palazzol/TMS7xxx_dumper/images/DatabookDescribingSimilarInterface1.jpg

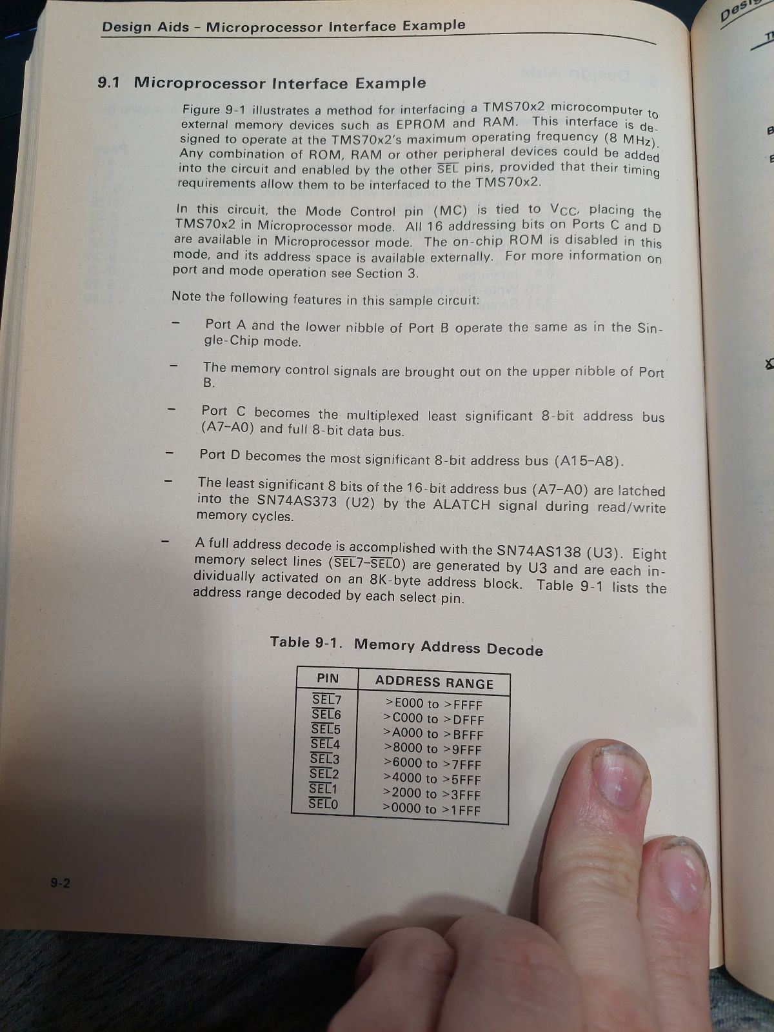
images/DatabookDescribingSimilarInterface1.jpg
