palazzol/TMS7xxx_dumper/images/DatabookDescribingSimilarInterface2.jpg

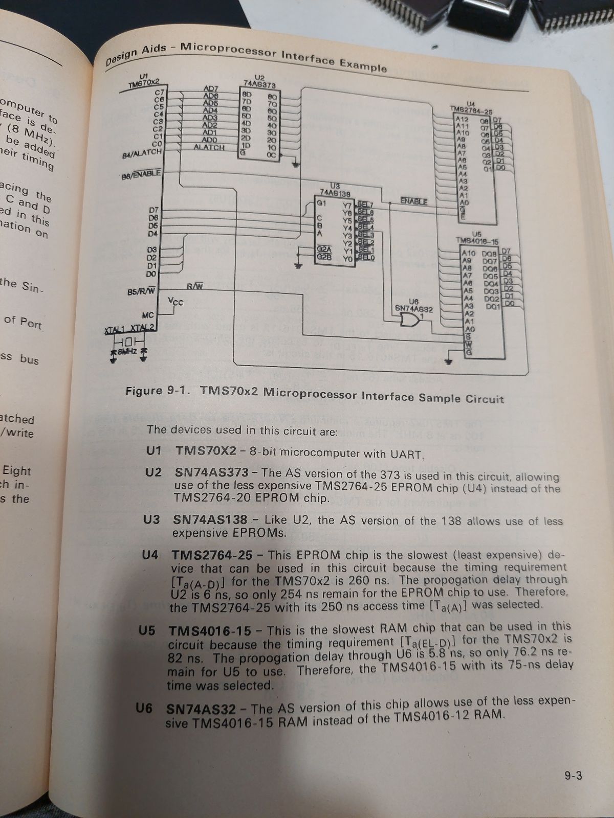
images/DatabookDescribingSimilarInterface2.jpg
