palazzol/TMS7xxx_dumper/images/latest databook excerpts/20230110_223147.jpg

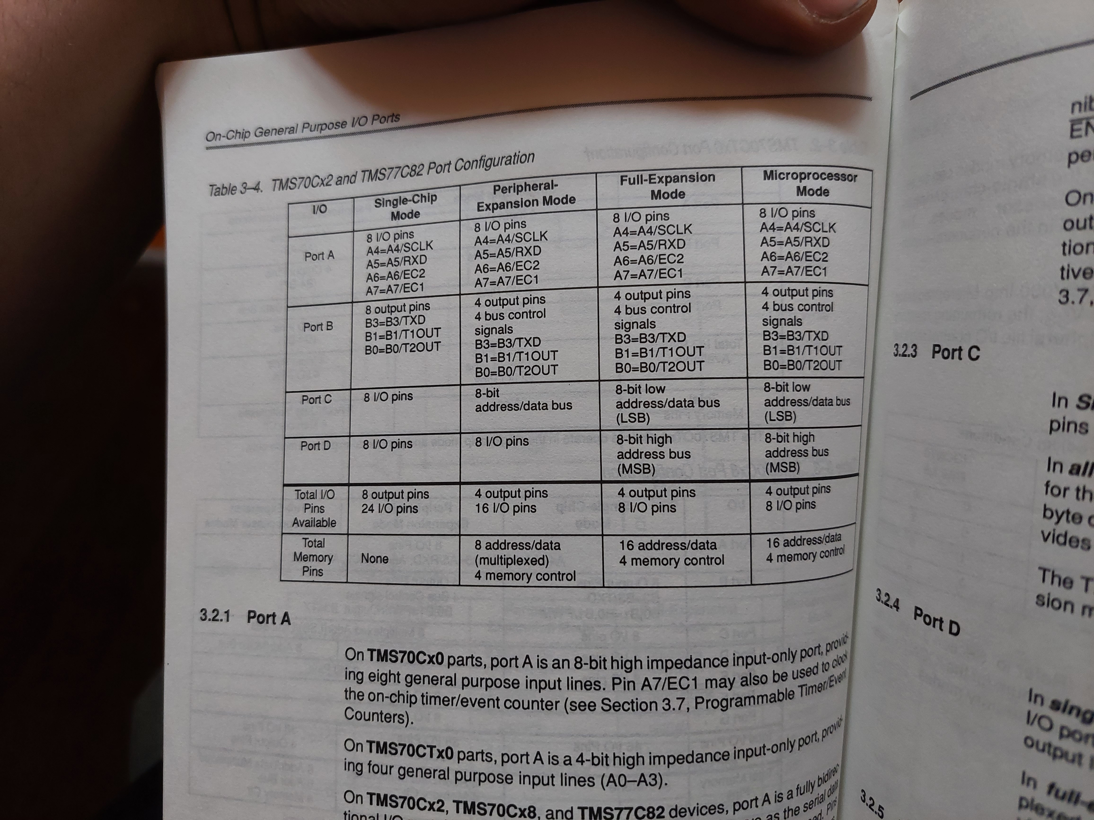
images/latest databook excerpts/20230110_223147.jpg
