palazzol/TMS7xxx_dumper/images/latest databook excerpts/20230110_223242.jpg

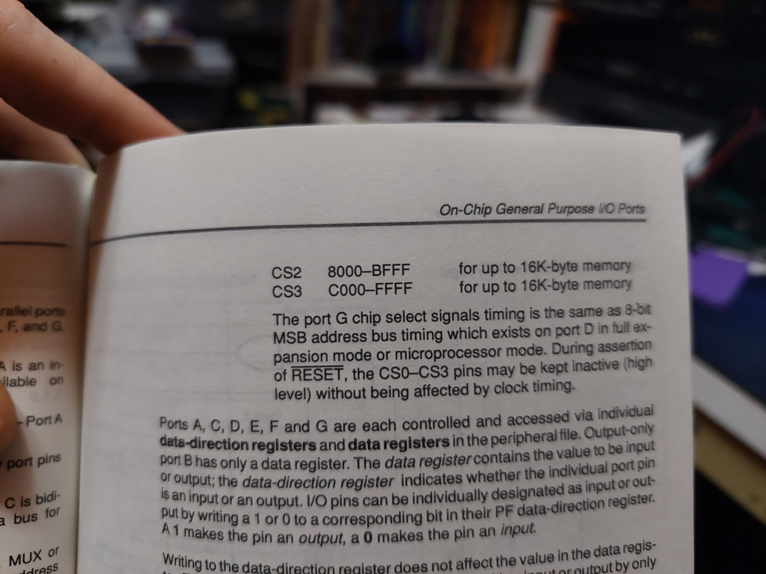
images/latest databook excerpts/20230110_223242.jpg
