palazzol/TMS7xxx_dumper/images/OriginalBoard_back.jpg

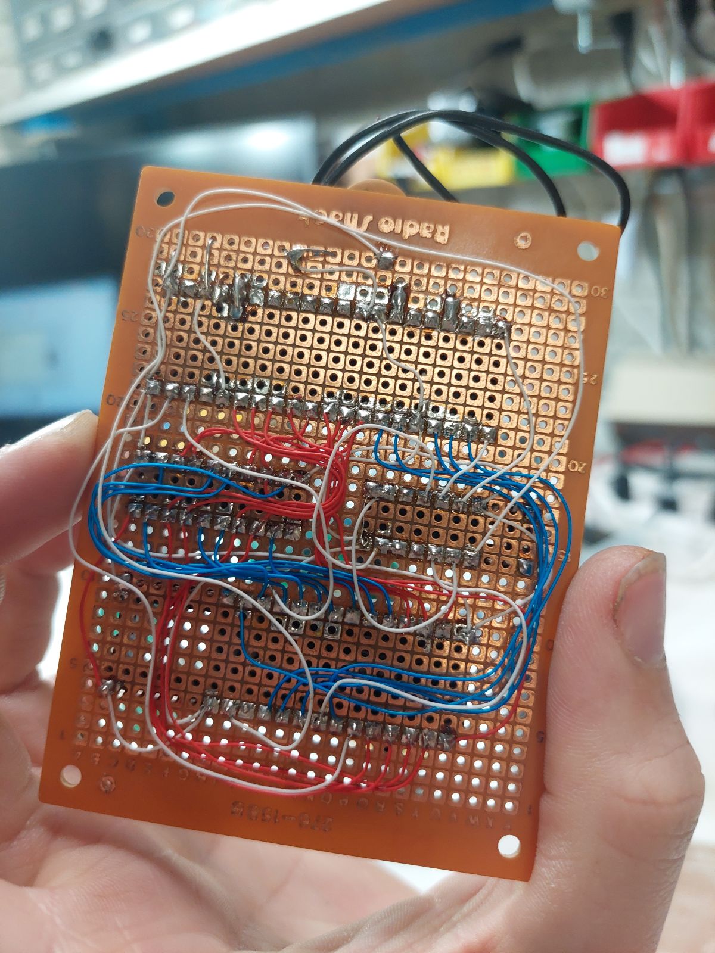
images/OriginalBoard_back.jpg
