palazzol/TMS7xxx_dumper/images/OriginalBoard_front.jpg

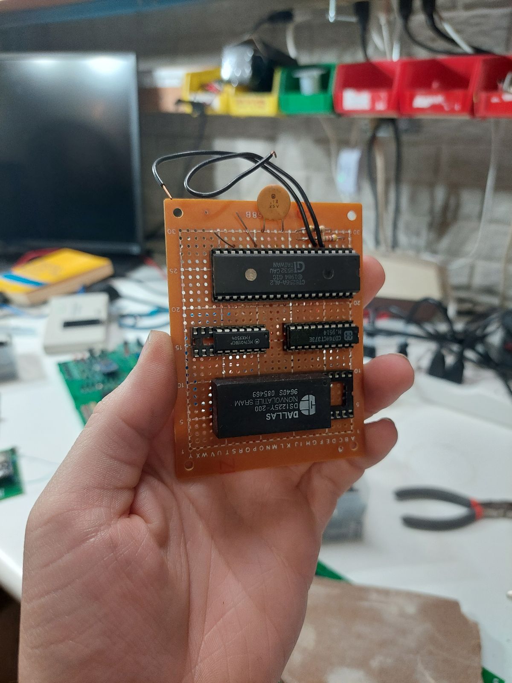
images/OriginalBoard_front.jpg
