palazzol/TMS7xxx_dumper/images/screenshots/chrome_HalUI1rVbq.png

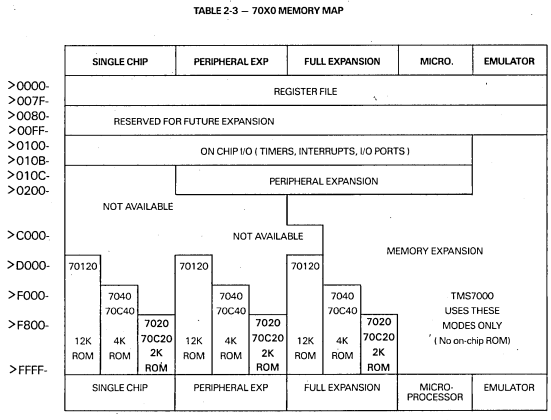
images/screenshots/chrome_HalUI1rVbq.png
