palazzol/TMS7xxx_dumper/images/screenshots/chrome_LtrWvr9aTm.png

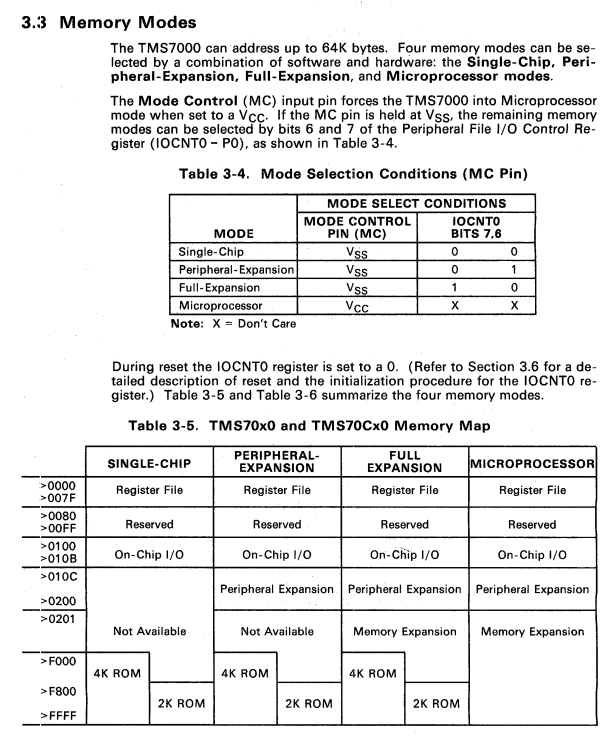
images/screenshots/chrome_LtrWvr9aTm.png
