palazzol/TMS7xxx_dumper/images/screenshots/chrome_wzu2HBYSrh.png

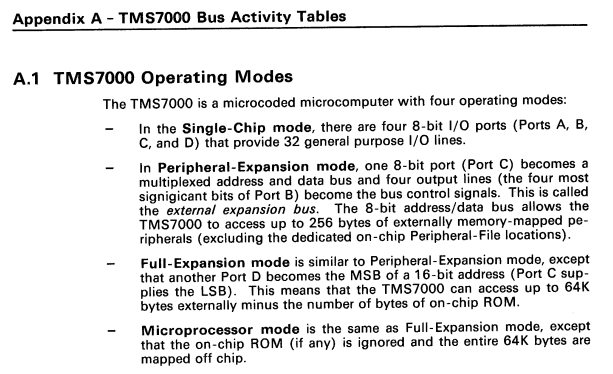
images/screenshots/chrome_wzu2HBYSrh.png
