palazzol/TMS7xxx_dumper/images/screenshots/chrome_Xs2TtNlXFw.png

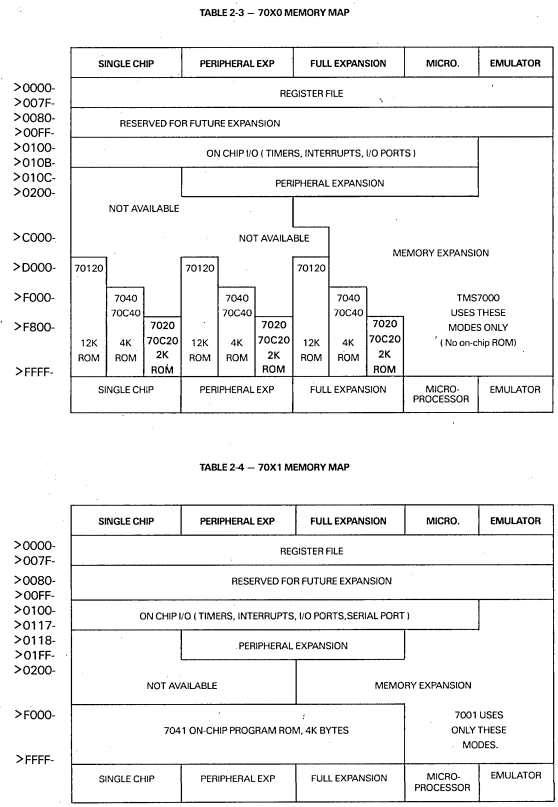
images/screenshots/chrome_Xs2TtNlXFw.png
