palazzol/TMS7xxx_dumper/images/screenshots/javaw_PXxrph4Tbt.png

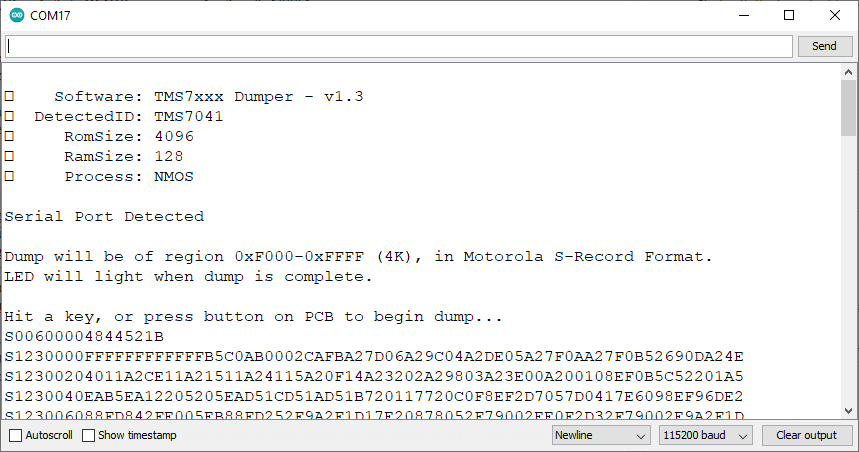
images/screenshots/javaw_PXxrph4Tbt.png
