palazzol/TMS7xxx_dumper/images/screenshots/kicad_Mz2W2un4fd.png

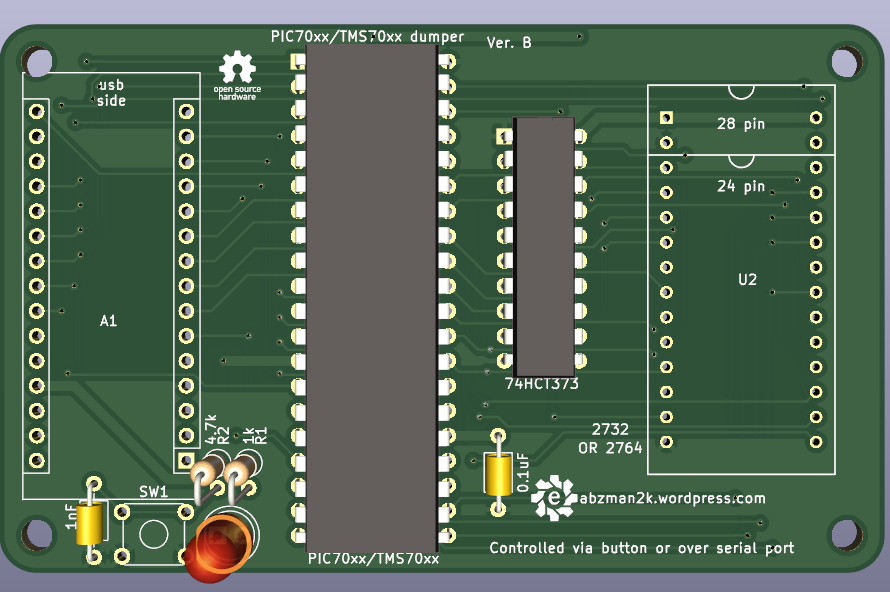
images/screenshots/kicad_Mz2W2un4fd.png
