palazzol/TMS7xxx_dumper/images/screenshots/kicad_PIJrje4ejr.png

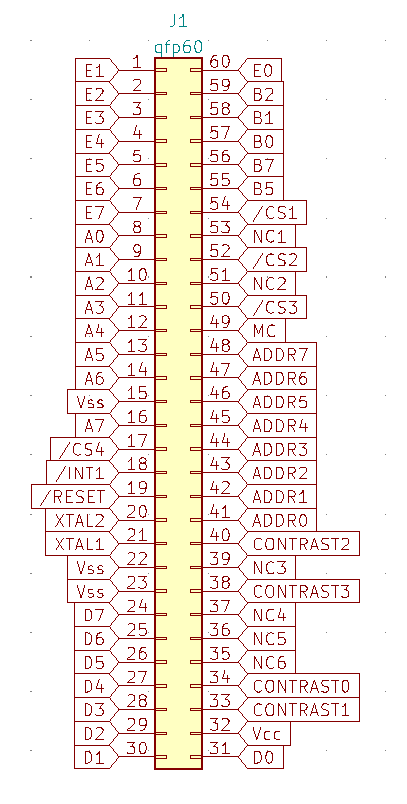
images/screenshots/kicad_PIJrje4ejr.png
