palazzol/TMS7xxx_dumper/images/screenshots/kicad_UQmzgc0r3t.png

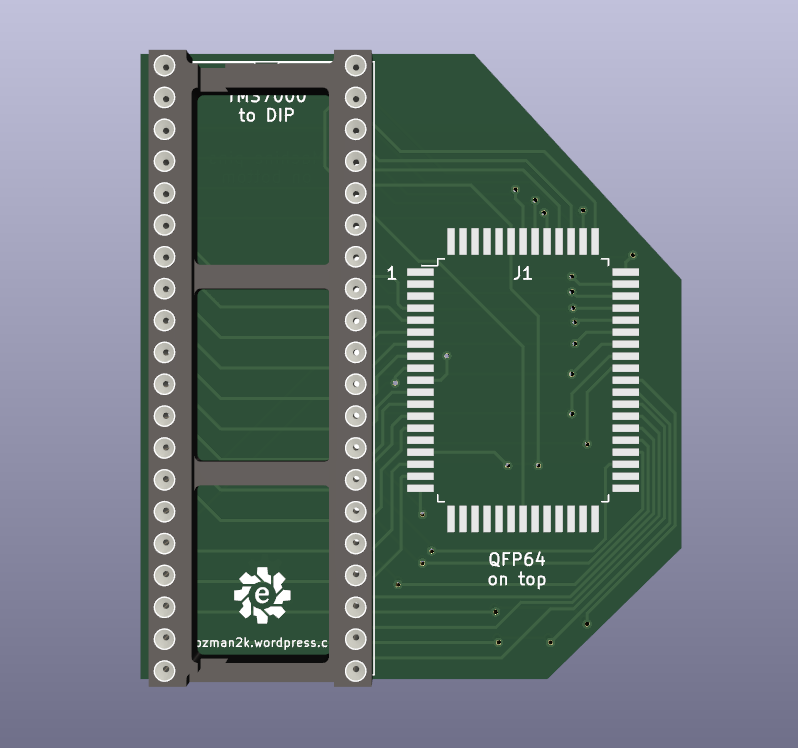
images/screenshots/kicad_UQmzgc0r3t.png
