palazzol/TMS7xxx_dumper/images/screenshots/NVIDIA_Share_yhMcKGZ78z.png

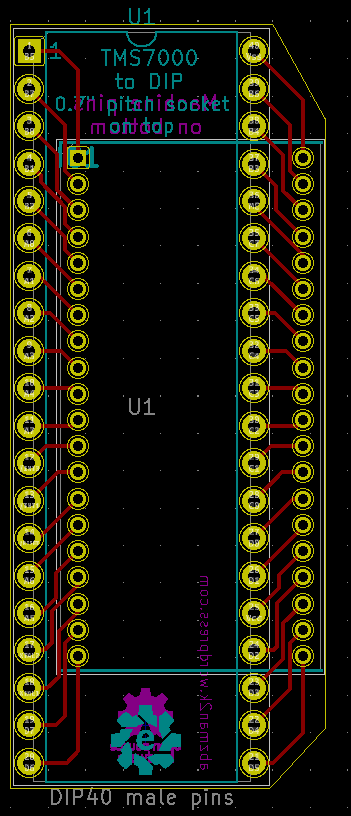
images/screenshots/NVIDIA_Share_yhMcKGZ78z.png
