palazzol/TMS7xxx_dumper/images/screenshots/pcbnew_1locTDAT6m.png

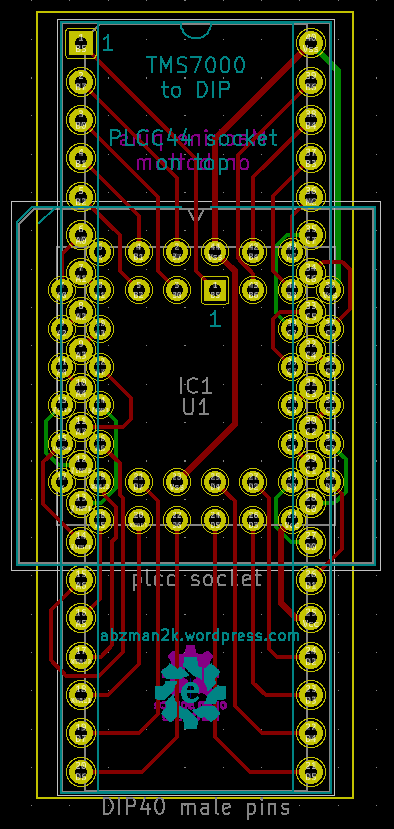
images/screenshots/pcbnew_1locTDAT6m.png
