palazzol/TMS7xxx_dumper/images/screenshots/soffice.bin_luXU2pbuv5.png

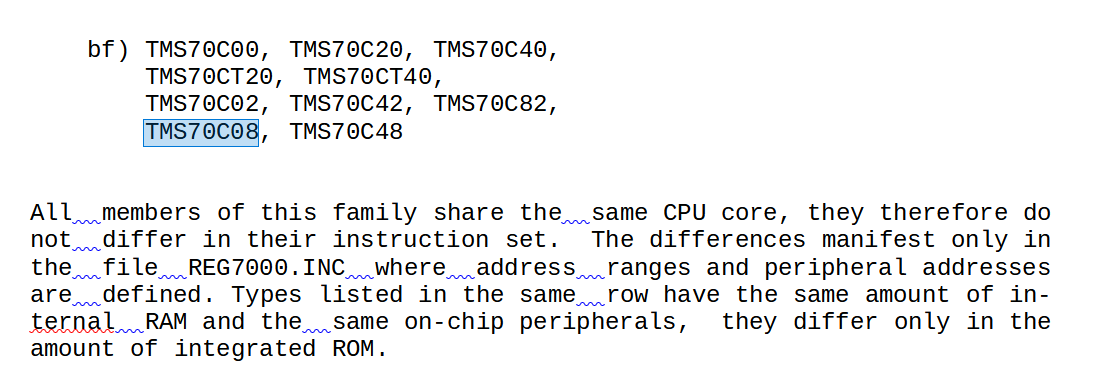
images/screenshots/soffice.bin_luXU2pbuv5.png
