palazzol/TMS7xxx_dumper/hardware/dumper/dumper.kicad_pcb

## KiCad design hardware/dumper/dumper.kicad_pcb (2023-01-10)

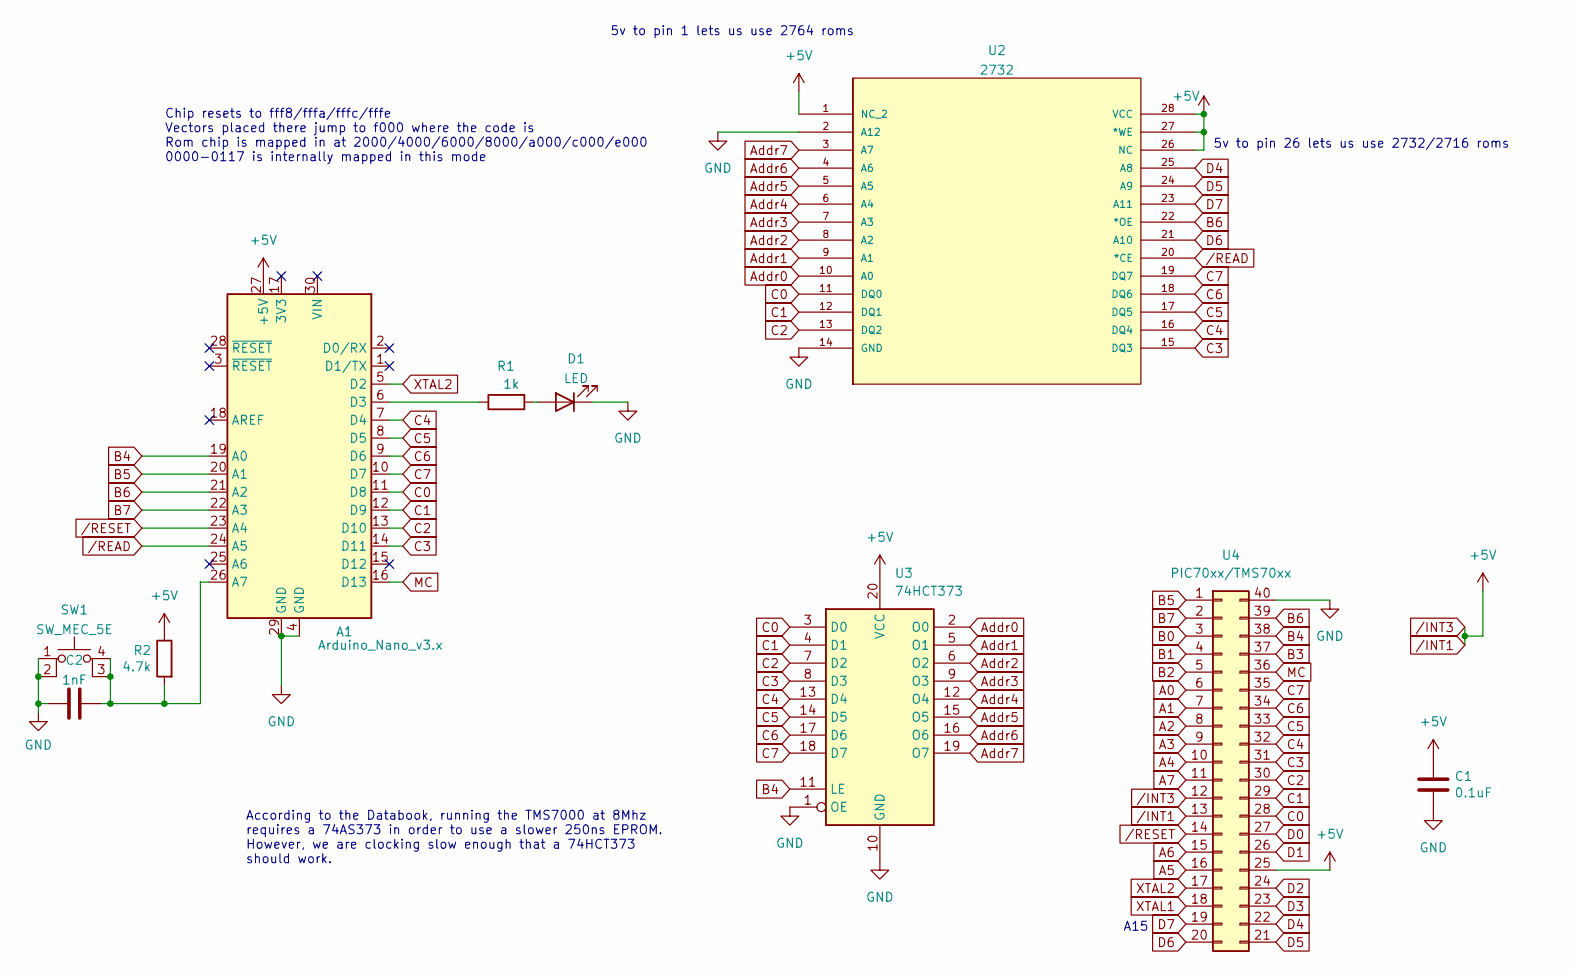
[picture p51: schematic dumper.kicad_sch]

Parts:
A1: Arduino_Nano_v3.x; Arduino_Nano
C1: 0.1uF; C_Axial_L3.8mm_D2.6mm_P7.50mm_Horizontal
C2: 1nF; C_Axial_L3.8mm_D2.6mm_P7.50mm_Horizontal
D1: LED; LED_D5.0mm
R1: 1k; R_Axial_DIN0207_L6.3mm_D2.5mm_P2.54mm_Vertical
R2: 4.7k; R_Axial_DIN0207_L6.3mm_D2.5mm_P2.54mm_Vertical
SW1: SW_MEC_5E; SW_TH_Tactile_Omron_B3F-10xx
U2: 2732; 21-0245A_28; MANUFACTURER_PART_NUMBER DS1225Y150+
U3: 74HCT373; DIP-20_W7.62mm
U4: PIC70xx/TMS70xx; DIP-40_W15.24mm

Connections:
A0: U4.6
A1: U4.7
A2: U4.8
A3: U4.9
A4: U4.10
A5: U4.16
A6: U4.15
A7: U4.11
Addr0: U2.10 (A0), U3.2 (O0)
Addr1: U2.9 (A1), U3.5 (O1)
Addr2: U2.8 (A2), U3.6 (O2)
Addr3: U2.7 (A3), U3.9 (O3)
Addr4: U2.6 (A4), U3.12 (O4)
Addr5: U2.5 (A5), U3.15 (O5)
Addr6: U2.4 (A6), U3.16 (O6)
Addr7: U2.3 (A7), U3.19 (O7)
B0: U4.3
B1: U4.4
B2: U4.5
B3: U4.37
B4: A1.19 (A0), U3.11 (LE), U4.38
B5: A1.20 (A1), U4.1
B6: A1.21 (A2), U2.22 (*OE), U4.39
B7: A1.22 (A3), U4.2
C0: A1.11 (D8), U2.11 (DQ0), U3.3 (D0), U4.28
C1: A1.12 (D9), U2.12 (DQ1), U3.4 (D1), U4.29
C2: A1.13 (D10), U2.13 (DQ2), U3.7 (D2), U4.30
C3: A1.14 (D11), U2.15 (DQ3), U3.8 (D3), U4.31
C4: A1.7 (D4), U2.16 (DQ4), U3.13 (D4), U4.32
C5: A1.8 (D5), U2.17 (DQ5), U3.14 (D5), U4.33
C6: A1.9 (D6), U2.18 (DQ6), U3.17 (D6), U4.34
C7: A1.10 (D7), U2.19 (DQ7), U3.18 (D7), U4.35
D0: U4.27
D1: U4.26
D2: U4.24
D3: U4.23
D4: U2.25 (A8), U4.22
D5: U2.24 (A9), U4.21
D6: U2.21 (A10), U4.20
D7: U2.23 (A11), U4.19
GND: A1.4 (GND), A1.29 (GND), C1.2, C2.1, D1.1 (K), SW1.1, SW1.2, U2.2 (A12), U2.14 (GND), U3.1 (OE), U3.10 (GND), U4.40
MC: A1.16 (D13), U4.36
unnamed: A1.6 (D3), R1.1
unnamed: A1.26 (A7), C2.2, R2.2, SW1.3 (K), SW1.4 (A)
unnamed: D1.2 (A), R1.2
XTAL1: U4.18
XTAL2: A1.5 (D2), U4.17
/INT1: A1.27 (+5V), C1.1, R2.1, U2.1 (NC_2), U2.26 (NC), U2.27 (*WE), U2.28 (VCC), U3.20 (VCC), U4.12, U4.13, U4.25
/READ: A1.24 (A5), U2.20 (*CE)
/RESET: A1.23 (A4), U4.14

Notes on the sheet:
According to the Databook, running the TMS7000 at 8Mhz requires a 74AS373 in order to use a slower 250ns EPROM. However, we are clocking slow enough that a 74HCT373 should work.
5v to pin 26 lets us use 2732/2716 roms
5v to pin 1 lets us use 2764 roms
Chip resets to fff8/fffa/fffc/fffe Vectors placed there jump to f000 where the code is Rom chip is mapped in at 2000/4000/6000/8000/a000/c000/e000 0000-0117 is internally mapped in this mode
A15

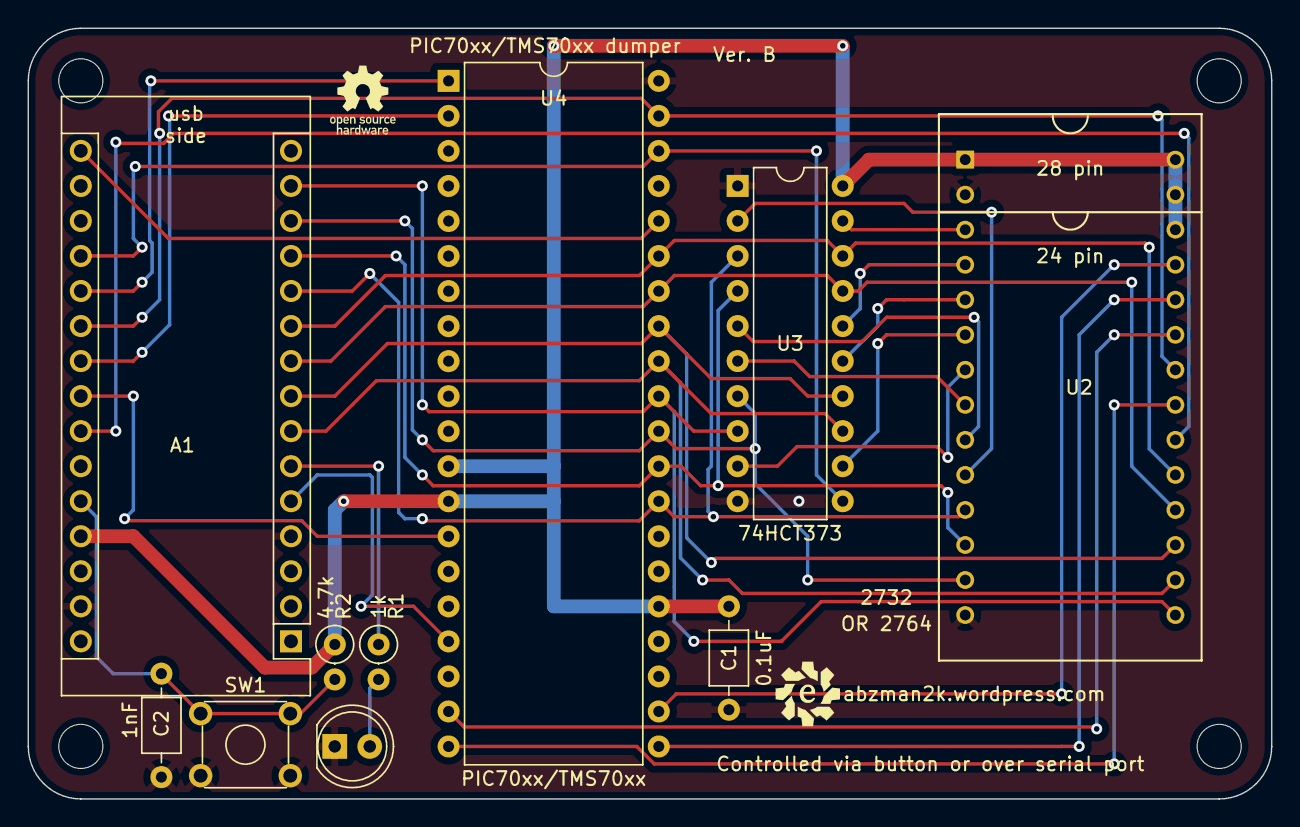
[picture p52: board hardware/dumper/dumper.kicad_pcb from above]

Board: 2 copper layers, 90.2 x 55.9 mm, 10 parts (0 on the bottom side), 33 nets.
