palazzol/TMS7xxx_dumper/software/other/fia10_rom.asm

4000: 8c 51 0d     BR $510D
4003: 8c 66 6f     BR $666F
4006: 8c 42 4f     BR $424F
4009: 8c 40 27     BR $4027
400c: 8c 40 27     BR $4027
400f: 8c 40 27     BR $4027
4012: 8c 40 27     BR $4027
4015: 8c 40 27     BR $4027
4018: 8c 40 27     BR $4027
401b: 8c 47 e0     BR $47E0
401e: 8c 40 28     BR $4028
4021: 8c 46 74     BR $4674
4024: 8c 4d 9a     BR $4D9A
4027: 0a           RETS
4028: a2 20 18     MOVP %>20,P24
402b: 72 16 27     MOV %>16,R39
402e: 8a 54 f9     LDA @>54F9
4031: 82 0f        MOVP A,P15
4033: 8a 54 fa     LDA @>54FA
4036: 82 0e        MOVP A,P14
4038: 22 a5        MOV %>A5,A
403a: 8d e0 00     CMPA @>E000
403d: e6 34        JNZ $4073
403f: be           RL A
4040: 8d e0 01     CMPA @>E001
4043: e6 2e        JNZ $4073
4045: be           RL A
4046: 8d e0 02     CMPA @>E002
4049: e6 28        JNZ $4073
404b: be           RL A
404c: 8d e0 03     CMPA @>E003
404f: e6 22        JNZ $4073
4051: b5           CLR A
4052: 8d ef fe     CMPA @>EFFE
4055: e6 1c        JNZ $4073
4057: b4           INV A
4058: 8d ef ff     CMPA @>EFFF
405b: e6 16        JNZ $4073
405d: 8e 55 19     CALL $5519
4060: 52 02        MOV %>2,B
4062: ce           RL B
4063: aa 54 f9     LDA @>54F9(B)
4066: 82 0f        MOVP A,P15
4068: aa 54 fa     LDA @>54FA(B)
406b: 82 0e        MOVP A,P14
406d: a2 38 18     MOVP %>38,P24
4070: 8c e0 04     BR $E004
4073: 8a 20 20     LDA @>2020
4076: 2d 6a        CMP %>6A,A
4078: e2 04        JEQ $407E
407a: 2d 95        CMP %>95,A
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
5e01: 10           Illegal Opcode
5e02: 23 40        AND %>40,A
5e04: 21           Illegal Opcode
5e05: 40           Illegal Opcode
5e06: 21           Illegal Opcode
5e07: 10           Illegal Opcode
5e08: 21           Illegal Opcode
5e09: 04           Illegal Opcode
5e0a: 23 10        AND %>10,A
5e0c: 27 04 27     BTJZ %>4,A,$5E36
5e0f: 40           Illegal Opcode
5e10: 25 40        XOR %>40,A
5e12: 1f 40        DSB R64,A
5e14: 1f 04        DSB R4,A
5e16: 23 04        AND %>4,A
5e18: 68           ADD B,A
5e19: 10           Illegal Opcode
5e1a: 68           ADD B,A
5e1b: 80 66        MOVP P102,A
5e1d: 80 6c        MOVP P108,A
5e1f: 02           Illegal Opcode
5e20: 6a           SUB B,A
5e21: 02           Illegal Opcode
5e22: 6a           SUB B,A
5e23: 08           POP ST
5e24: 6c           MPY B,A
5e25: 08           POP ST
5e26: 66 10        BTJO B,A,$5E38
5e28: 26 08 68     BTJO %>8,A,$5E93
5e2b: 20           Illegal Opcode
5e2c: 66 20        BTJO B,A,$5E4E
5e2e: 64           OR B,A
5e2f: 20           Illegal Opcode
5e30: 6a           SUB B,A
5e31: 01           IDLE
5e32: 6c           MPY B,A
5e33: 01           IDLE
5e34: 6a           SUB B,A
5e35: 10           Illegal Opcode
5e36: 6a           SUB B,A
5e37: 80 6a        MOVP P106,A
5e39: 20           Illegal Opcode
5e3a: 6c           MPY B,A
5e3b: 80 6d        MOVP P109,A
5e3d: 20           Illegal Opcode
5e3e: 6b           SBB B,A
5e3f: 80 6d        MOVP P109,A
5e41: 80 6c        MOVP P108,A
5e43: 10           Illegal Opcode
5e44: 64           OR B,A
5e45: 10           Illegal Opcode
5e46: 64           OR B,A
5e47: 80 6c        MOVP P108,A
5e49: 20           Illegal Opcode
5e4a: 6b           SBB B,A
5e4b: 20           Illegal Opcode
5e4c: 6b           SBB B,A
5e4d: 10           Illegal Opcode
5e4e: 6d           CMP B,A
5e4f: 10           Illegal Opcode
5e50: 67 10        BTJZ B,A,$5E62
5e52: 69           ADC B,A
5e53: 80 67        MOVP P103,A
5e55: 80 65        MOVP P101,A
5e57: 20           Illegal Opcode
5e58: 63           AND B,A
5e59: 20           Illegal Opcode
5e5a: 63           AND B,A
5e5b: 80 63        MOVP P99,A
5e5d: 10           Illegal Opcode
5e5e: 65           XOR B,A
5e5f: 80 69        MOVP P105,A
5e61: 10           Illegal Opcode
5e62: 69           ADC B,A
5e63: 20           Illegal Opcode
5e64: 67 20        BTJZ B,A,$5E86
5e66: 61           Illegal Opcode
5e67: 20           Illegal Opcode
5e68: 61           Illegal Opcode
5e69: 10           Illegal Opcode
5e6a: 65           XOR B,A
5e6b: 10           Illegal Opcode
5e6c: 52 02        MOV %>2,B
5e6e: 68           ADD B,A
5e6f: 40           Illegal Opcode
5e70: 66 40        BTJO B,A,$5EB2
5e72: 40           Illegal Opcode
5e73: 40           Illegal Opcode
5e74: 3e 40        DAC R64,B
5e76: 6a           SUB B,A
5e77: 04           Illegal Opcode
5e78: 6c           MPY B,A
5e79: 04           Illegal Opcode
5e7a: 50           Illegal Opcode
5e7b: 02           Illegal Opcode
5e7c: 26 80 52     BTJO %>80,A,$5ED1
5e7f: 40           Illegal Opcode
5e80: 50           Illegal Opcode
5e81: 40           Illegal Opcode
5e82: 4e 40 3e     DAC R64,R62
5e85: 02           Illegal Opcode
5e86: 40           Illegal Opcode
5e87: 02           Illegal Opcode
5e88: 54 02        OR %>2,B
5e8a: 6a           SUB B,A
5e8b: 40           Illegal Opcode
5e8c: 54 40        OR %>40,B
5e8e: 6c           MPY B,A
5e8f: 40           Illegal Opcode
5e90: 57 40 6b     BTJZ %>40,B,$5EFE
5e93: 40           Illegal Opcode
5e94: 6d           CMP B,A
5e95: 40           Illegal Opcode
5e96: 56 02 4e     BTJO %>2,B,$5EE7
5e99: 02           Illegal Opcode
5e9a: 64           OR B,A
5e9b: 40           Illegal Opcode
5e9c: 56 40 55     BTJO %>40,B,$5EF4
5e9f: 40           Illegal Opcode
5ea0: 55 02        XOR %>2,B
5ea2: 57 02 51     BTJZ %>2,B,$5EF6
5ea5: 02           Illegal Opcode
5ea6: 69           ADC B,A
5ea7: 40           Illegal Opcode
5ea8: 67 40        BTJZ B,A,$5EEA
5eaa: 4f 40 4d     DSB R64,R77
5ead: 40           Illegal Opcode
5eae: 63           AND B,A
5eaf: 40           Illegal Opcode
5eb0: 4d 02 65     CMP R2,R101
5eb3: 40           Illegal Opcode
5eb4: 53 02        AND %>2,B
5eb6: 53 40        AND %>40,B
5eb8: 51           Illegal Opcode
5eb9: 40           Illegal Opcode
5eba: 4b 40 4b     SBB R64,R75
5ebd: 02           Illegal Opcode
5ebe: 4f 02 52     DSB R2,R82
5ec1: 08           POP ST
5ec2: 52 20        MOV %>20,B
5ec4: 50           Illegal Opcode
5ec5: 20           Illegal Opcode
5ec6: 40           Illegal Opcode
5ec7: 80 3e        MOVP P62,A
5ec9: 80 3e        MOVP P62,A
5ecb: 20           Illegal Opcode
5ecc: 40           Illegal Opcode
5ecd: 20           Illegal Opcode
5ece: 50           Illegal Opcode
5ecf: 08           POP ST
5ed0: 26 01 52     BTJO %>1,A,$5F25
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
5fce: 1a 80        SUB R128,A
5fd0: 18 80        ADD R128,A
5fd2: 16 08 16     BTJO R8,A,$5FEB
5fd5: 01           IDLE
5fd6: 18 01        ADD R1,A
5fd8: 10           Illegal Opcode
5fd9: 20           Illegal Opcode
5fda: 10           Illegal Opcode
5fdb: 02           Illegal Opcode
5fdc: 10           Illegal Opcode
5fdd: 08           POP ST
5fde: 0e           PUSH ST
5fdf: 02           Illegal Opcode
5fe0: 0e           PUSH ST
5fe1: 08           POP ST
5fe2: 0c           Illegal Opcode
5fe3: 02           Illegal Opcode
5fe4: 0c           Illegal Opcode
5fe5: 20           Illegal Opcode
5fe6: 0e           PUSH ST
5fe7: 20           Illegal Opcode
5fe8: 10           Illegal Opcode
5fe9: 01           IDLE
5fea: 10           Illegal Opcode
5feb: 80 0e        MOVP P14,A
5fed: 80 0c        MOVP P12,A
5fef: 08           POP ST
5ff0: 0c           Illegal Opcode
5ff1: 01           IDLE
5ff2: 0e           PUSH ST
5ff3: 01           IDLE
5ff4: 0a           RETS
5ff5: 20           Illegal Opcode
5ff6: 0a           RETS
5ff7: 02           Illegal Opcode
5ff8: 0a           RETS
5ff9: 08           POP ST
5ffa: 08           POP ST
5ffb: 02           Illegal Opcode
5ffc: 08           POP ST
5ffd: 08           POP ST
5ffe: 06           DINT
5fff: 02           Illegal Opcode
6000: 06           DINT
6001: 20           Illegal Opcode
6002: 08           POP ST
6003: 20           Illegal Opcode
6004: 0a           RETS
6005: 01           IDLE
6006: 0a           RETS
6007: 80 08        MOVP P8,A
6009: 80 06        MOVP P6,A
600b: 08           POP ST
600c: 06           DINT
600d: 01           IDLE
600e: 08           POP ST
600f: 01           IDLE
6010: 11           Illegal Opcode
6011: 20           Illegal Opcode
6012: 11           Illegal Opcode
6013: 02           Illegal Opcode
6014: 11           Illegal Opcode
6015: 08           POP ST
6016: 0f           Illegal Opcode
6017: 02           Illegal Opcode
6018: 0f           Illegal Opcode
6019: 08           POP ST
601a: 0d           LDSP
601b: 02           Illegal Opcode
601c: 0d           LDSP
601d: 20           Illegal Opcode
601e: 0f           Illegal Opcode
601f: 20           Illegal Opcode
6020: 11           Illegal Opcode
6021: 01           IDLE
6022: 11           Illegal Opcode
6023: 80 0f        MOVP P15,A
6025: 80 0d        MOVP P13,A
6027: 08           POP ST
6028: 0d           LDSP
6029: 01           IDLE
602a: 0f           Illegal Opcode
602b: 01           IDLE
602c: 0b           RETI
602d: 20           Illegal Opcode
602e: 0b           RETI
602f: 02           Illegal Opcode
6030: 0b           RETI
6031: 08           POP ST
6032: 09           STSP
6033: 02           Illegal Opcode
6034: 09           STSP
6035: 08           POP ST
6036: 07           SETC
6037: 02           Illegal Opcode
6038: 07           SETC
6039: 20           Illegal Opcode
603a: 09           STSP
603b: 20           Illegal Opcode
603c: 0b           RETI
603d: 01           IDLE
603e: 0b           RETI
603f: 80 09        MOVP P9,A
6041: 80 07        MOVP P7,A
6043: 08           POP ST
6044: 07           SETC
6045: 01           IDLE
6046: 09           STSP
6047: 01           IDLE
6048: 05           EINT
6049: 20           Illegal Opcode
604a: 05           EINT
604b: 02           Illegal Opcode
604c: 05           EINT
604d: 08           POP ST
604e: 03           Illegal Opcode
604f: 02           Illegal Opcode
6050: 03           Illegal Opcode
6051: 08           POP ST
6052: 01           IDLE
6053: 02           Illegal Opcode
6054: 01           IDLE
6055: 20           Illegal Opcode
6056: 03           Illegal Opcode
6057: 20           Illegal Opcode
6058: 05           EINT
6059: 01           IDLE
605a: 05           EINT
605b: 80 03        MOVP P3,A
605d: 80 01        MOVP P1,A
605f: 08           POP ST
6060: 01           IDLE
6061: 01           IDLE
6062: 03           Illegal Opcode
6063: 01           IDLE
6064: fb           TRAP 4
6065: 88 60 bd 01  MOVD %>60BD,R1
6069: 8e 56 9d     CALL $569D
606c: 8e 58 76     CALL $5876
606f: 8e 57 81     CALL $5781
6072: 8e 4d 9a     CALL $4D9A
6075: 7d 31 76     CMP %>31,R118
6078: e6 05        JNZ $607F
607a: 75 01 32     XOR %>1,R50
607d: e0 f0        JMP $606F
607f: 73 bf 32     AND %>BF,R50
6082: 8e 60 9a     CALL $609A
6085: e6 0d        JNZ $6094
6087: 74 40 32     OR %>40,R50
608a: 88 60 c9 01  MOVD %>60C9,R1
608e: 8e 56 9d     CALL $569D
6091: 8e 58 76     CALL $5876
6094: 52 01        MOV %>1,B
6096: 0d           LDSP
6097: 8c 40 c7     BR $40C7
609a: 88 60 b1 29  MOVD %>60B1,R41
609e: 52 05        MOV %>5,B
60a0: 12 76        MOV R118,A
60a2: e0 02        JMP $60A6
60a4: db 29        DECD R41
60a6: 9d 29        CMPA *R41
60a8: e2 02        JEQ $60AC
60aa: ca f8        DJNZ B,$60A4
60ac: 0a           RETS
60ad: 1b 1c        SBB R28,A
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
62c0: 88 20 5f 75  MOVD %>205F,R117
62c4: b9           POP A
62c5: c9           POP B
62c6: b8           PUSH A
62c7: c8           PUSH B
62c8: be           RL A
62c9: be           RL A
62ca: be           RL A
62cb: 48 00 75     ADD R0,R117
62ce: 79 00 74     ADC %>0,R116
62d1: f6           TRAP 9
62d2: c9           POP B
62d3: c2           DEC B
62d4: 62           MOV B,A
62d5: ce           RL B
62d6: 38 00        ADD R0,B
62d8: ae 65 15     CALL @>6515(B)
62db: 8e 47 ff     CALL $47FF
62de: fa           TRAP 5
62df: 8c 61 f0     BR $61F0
62e2: fb           TRAP 4
62e3: 8e 42 45     CALL $4245
62e6: 8e 57 81     CALL $5781
62e9: 8e 4d 9a     CALL $4D9A
62ec: 7d 31 76     CMP %>31,R118
62ef: e6 05        JNZ $62F6
62f1: 75 01 32     XOR %>1,R50
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
