palazzol/TMS7xxx_dumper/software/orig/dumper_orig_disassembled.asm

f000: a2 ff 06     MOVP %>FF,P6
f003: 52 0c        MOV %>C,B
f005: 0d           LDSP
f006: 88 f0 30 05  MOVD %>F030,R5
f00a: 88 00 2c 07  MOVD %>002C,R7
f00e: 9a 05        LDA *R5
f010: 9b 07        STA *R7
f012: d3 07        INC R7
f014: 79 00 06     ADC %>0,R6
f017: d3 05        INC R5
f019: 79 00 04     ADC %>0,R4
f01c: 7d f0 04     CMP %>F0,R4
f01f: e6 ed        JNZ $F00E
f021: 7d 83 05     CMP %>83,R5
f024: e6 e8        JNZ $F00E
f026: 88 f1 00 07  MOVD %>F100,R7
f02a: 72 01 0a     MOV %>1,R10
f02d: 8c 00 2c     BR $002C
f030: a2 fe 06     MOVP %>FE,P6
f033: 52 ff        MOV %>FF,B
f035: c2           DEC B
f036: e6 fd        JNZ $F035
f038: 88 f0 00 05  MOVD %>F000,R5
f03c: 88 00 00 09  MOVD %>0000,R9
f040: 9a 05        LDA *R5
f042: 48 00 09     ADD R0,R9
f045: 79 00 08     ADC %>0,R8
f048: 72 08 02     MOV %>8,R2
f04b: bc           RR A
f04c: e3 05        JHS $F053
f04e: a3 fd 06     ANDP %>FD,P6
f051: e0 03        JMP $F056
f053: a4 02 06     ORP %>02,P6
f056: 52 10        MOV %>10,B
f058: c2           DEC B
f059: e6 fd        JNZ $F058
f05b: a3 fb 06     ANDP %>FB,P6
f05e: 52 10        MOV %>10,B
f060: c2           DEC B
f061: e6 fd        JNZ $F060
f063: a4 04 06     ORP %>04,P6
f066: d2 02        DEC R2
f068: e6 e1        JNZ $F04B
f06a: d3 05        INC R5
f06c: 79 00 04     ADC %>0,R4
f06f: e6 cf        JNZ $F040
f071: 12 08        MOV R8,A
f073: 9b 07        STA *R7
f075: d3 07        INC R7
f077: 12 09        MOV R9,A
f079: 9b 07        STA *R7
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
fff0: 00           NOP
fff1: 00           NOP
fff2: 00           NOP
fff3: 00           NOP
fff4: 00           NOP
fff5: 00           NOP
fff6: 00           NOP
fff7: 00           NOP
fff8: f0           TRAP 15
fff9: 00           NOP
fffa: f0           TRAP 15
fffb: 00           NOP
fffc: f0           TRAP 15
fffd: 00           NOP
fffe: f0           TRAP 15
ffff: 00           NOP
